geoffder/dometyl-keyboard/things/splaytyl/images/splaytyl_mt3.png

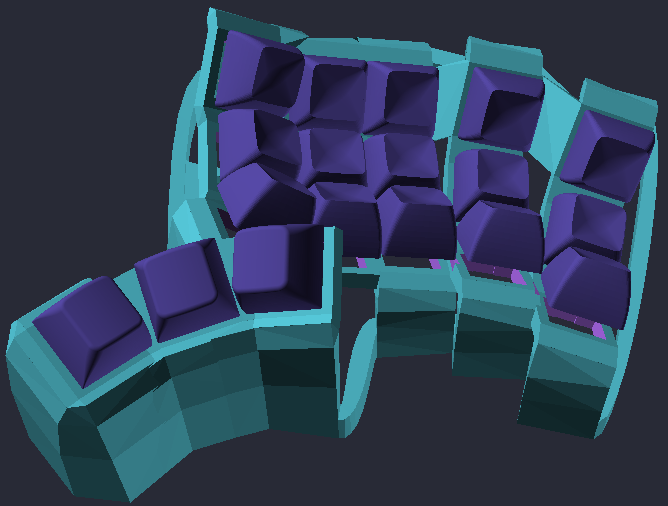
things/splaytyl/images/splaytyl_mt3.png
