geoffder/dometyl-keyboard/assets/sockets/mx_hotswap.stl

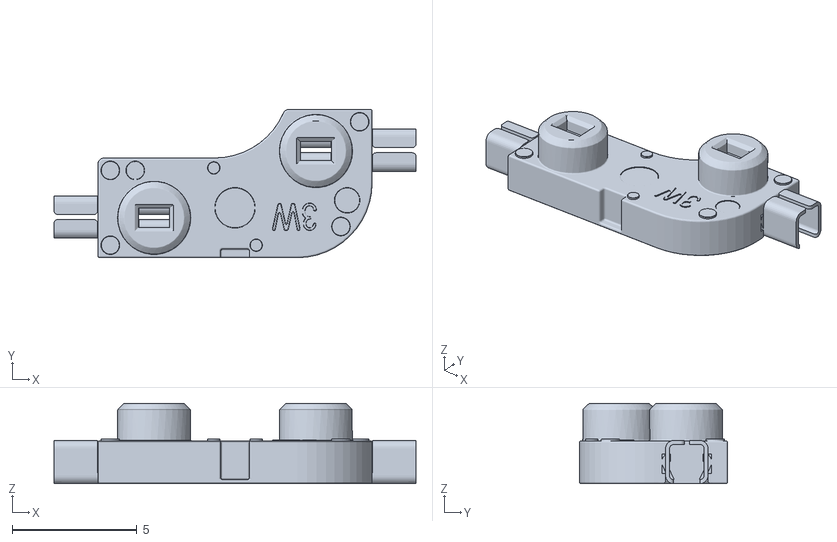
[picture p45: CAD file, 2021-09-09]
assets/sockets/mx_hotswap.stl
14.5 x 5.95 x 3.22
