geoffder/dometyl-keyboard/assets/switches/kailh_choc.stl

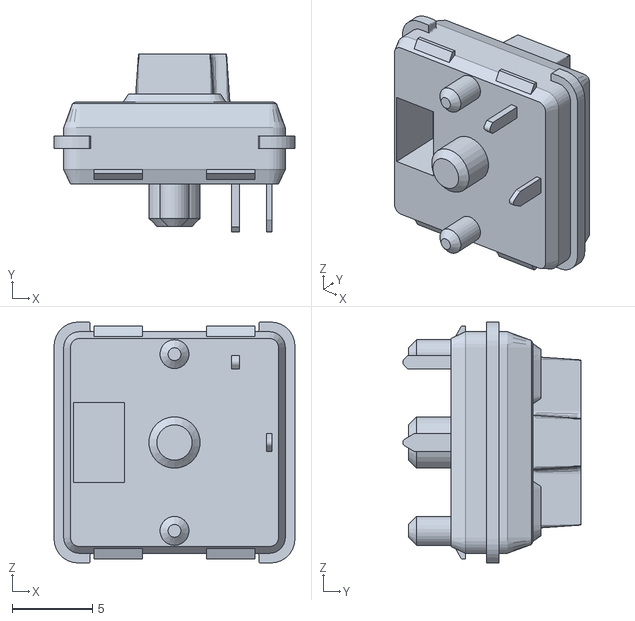
[picture p46: CAD file, 2021-09-06]
assets/switches/kailh_choc.stl
15.0 x 11.1 x 15.0
