geoffder/dometyl-keyboard/things/boards/choc_skeletyl/choc_skeletyl_right.stl

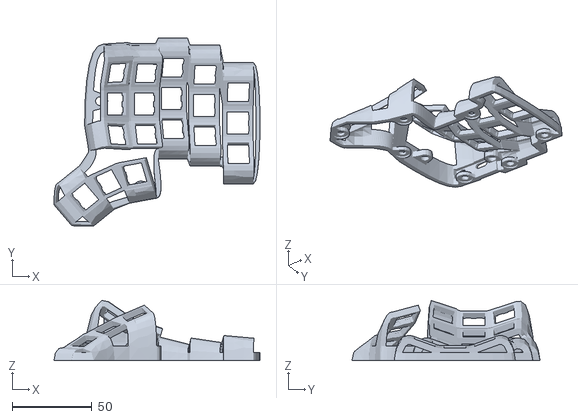
[picture p47: CAD file, 2021-11-04]
things/boards/choc_skeletyl/choc_skeletyl_right.stl
129.2 x 118.0 x 37.7
