geoffder/dometyl-keyboard/things/boards/choctyl/choctyl_hotswap_right.stl

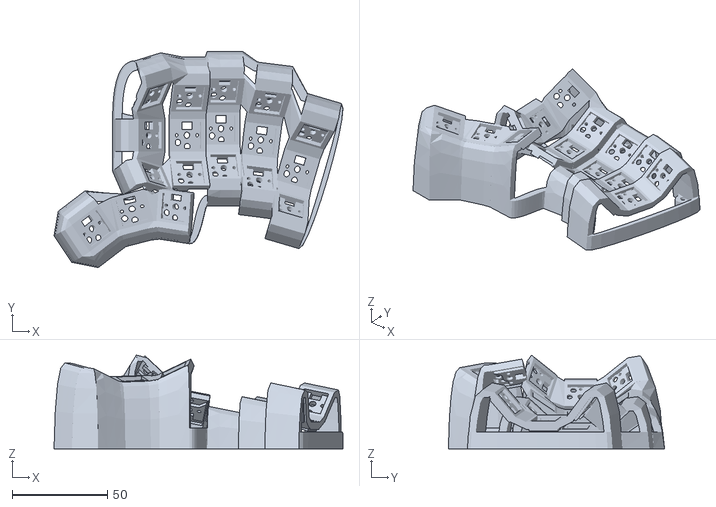
[picture p48: CAD file, 2021-11-10]
things/boards/choctyl/choctyl_hotswap_right.stl
151.9 x 113.6 x 49.3
