geoffder/dometyl-keyboard/things/boards/closed_splaytyl/closed_splaytyl_hotswap_left.stl

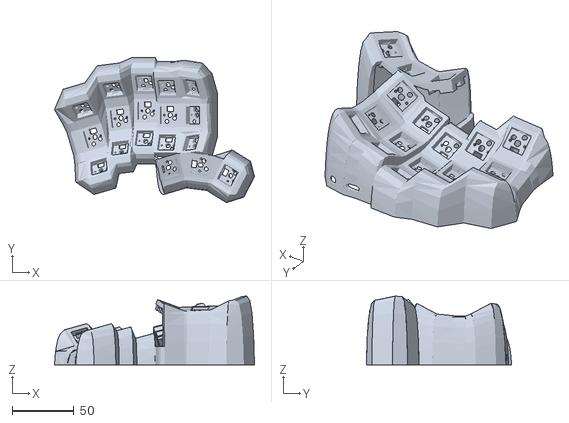
[picture p49: CAD file, 2021-09-25]
things/boards/closed_splaytyl/closed_splaytyl_hotswap_left.stl
161.5 x 117.4 x 55.7
