geoffder/dometyl-keyboard/things/boards/dartyl_choc/dartyl_mx.stl

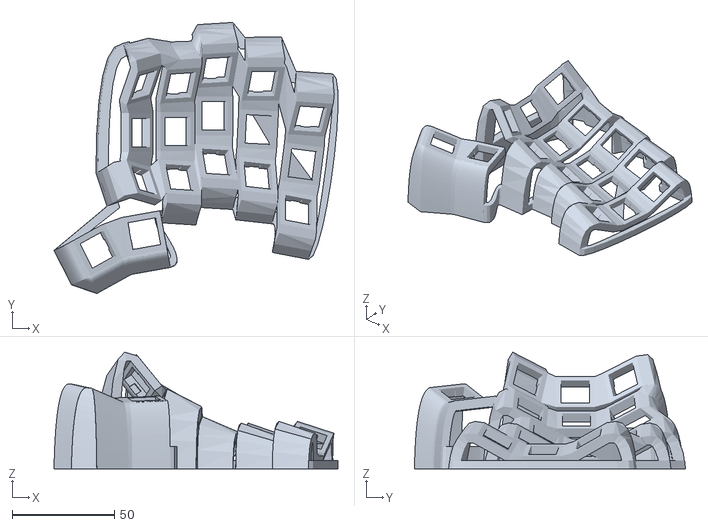
[picture p50: CAD file, 2021-11-20]
things/boards/dartyl_choc/dartyl_mx.stl
139.0 x 132.8 x 57.1
