geoffder/dometyl-keyboard/things/boards/dartyl_mx/dartyl_mx.stl

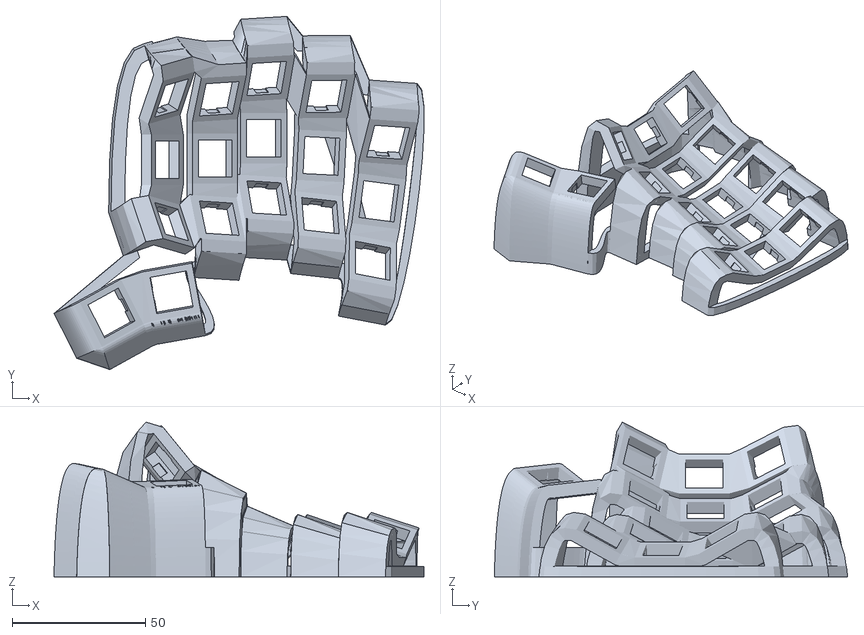
[picture p51: CAD file, 2021-11-20]
things/boards/dartyl_mx/dartyl_mx.stl
139.0 x 132.8 x 58.1
