geoffder/dometyl-keyboard/things/boards/niztyl/niztyl_right.stl

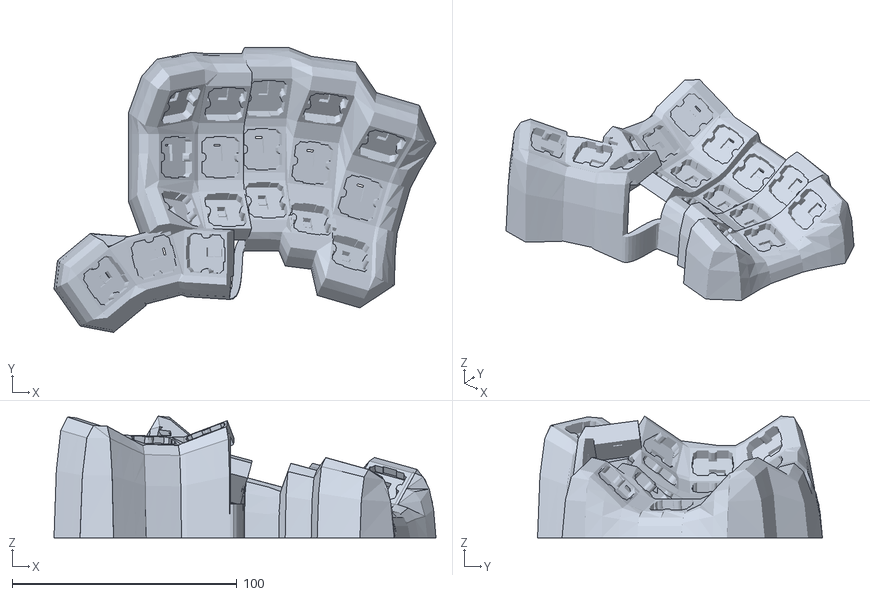
[picture p52: CAD file, 2021-11-09]
things/boards/niztyl/niztyl_right.stl
169.8 x 126.6 x 54.2
