geoffder/dometyl-keyboard/things/boards/splaytyl/splaytyl_tent_20deg_right.stl

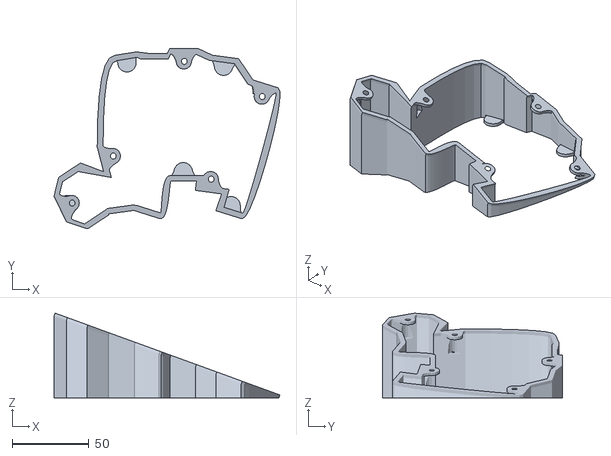
[picture p53: CAD file, 2021-10-03]
things/boards/splaytyl/splaytyl_tent_20deg_right.stl
147.0 x 117.4 x 55.1
