geoffder/dometyl-keyboard/things/choc_skeletyl/choc_skeletyl_right.stl

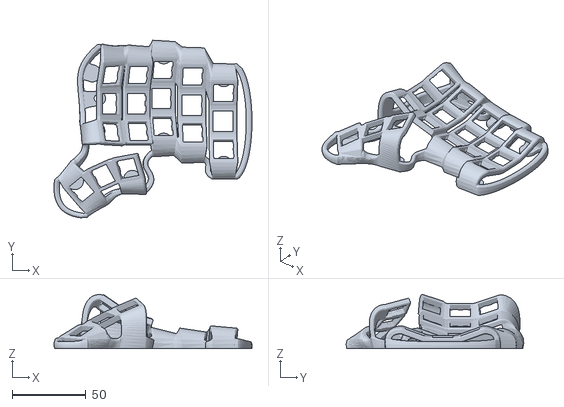
[picture p54: CAD file, 2023-01-07]
things/choc_skeletyl/choc_skeletyl_right.stl
134.2 x 120.4 x 36.9
