geoffder/dometyl-keyboard/things/dartyl_choc/usb_holder.stl

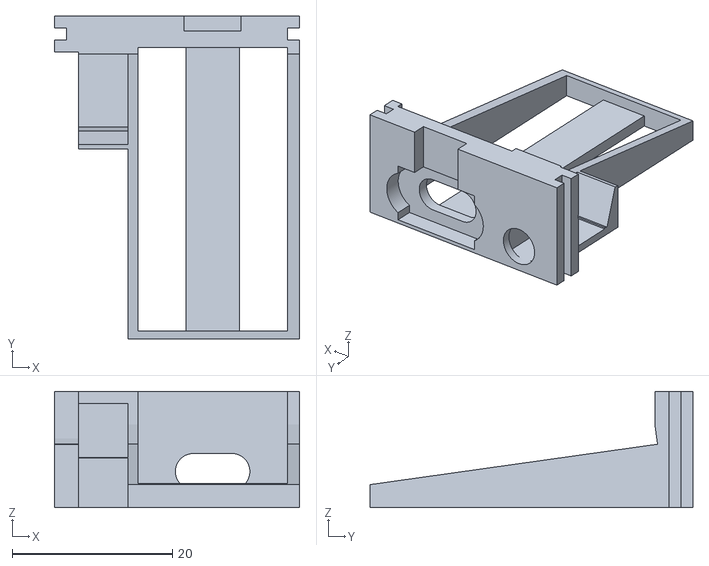
[picture p55: CAD file, 2021-11-20]
things/dartyl_choc/usb_holder.stl
30.6 x 40.3 x 14.5
