geoffder/dometyl-keyboard/things/dartyl_mx/MX_DES_Convex_012tol.stl

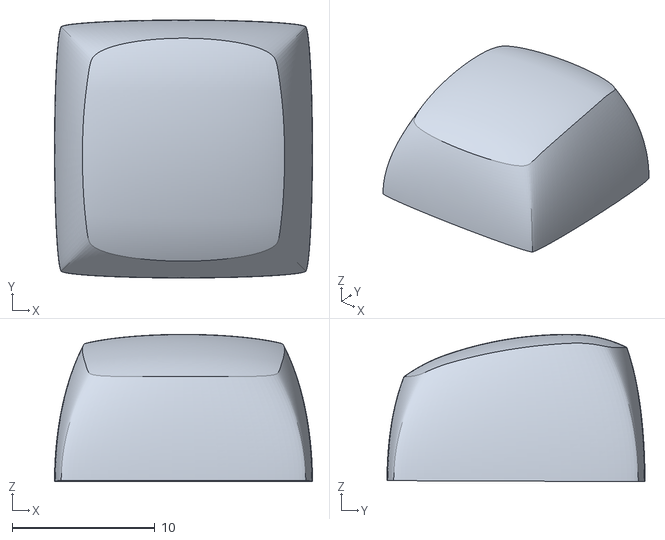
[picture p56: CAD file, 2021-11-20]
things/dartyl_mx/MX_DES_Convex_012tol.stl
18.1 x 18.1 x 10.3
