geoffder/dometyl-keyboard/things/niztyl/niztyl_base_right.stl

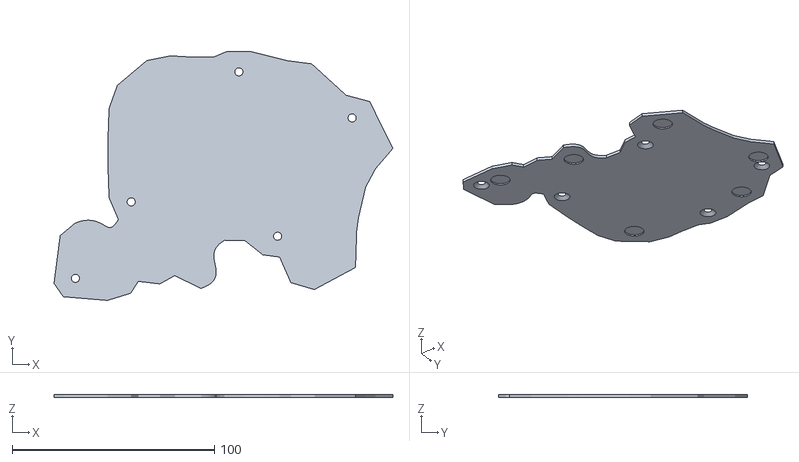
[picture p57: CAD file, 2023-01-07]
things/niztyl/niztyl_base_right.stl
167.8 x 123.1 x 1.65
