geoffder/dometyl-keyboard/things/splaytyl/splaytyl_base_right.stl

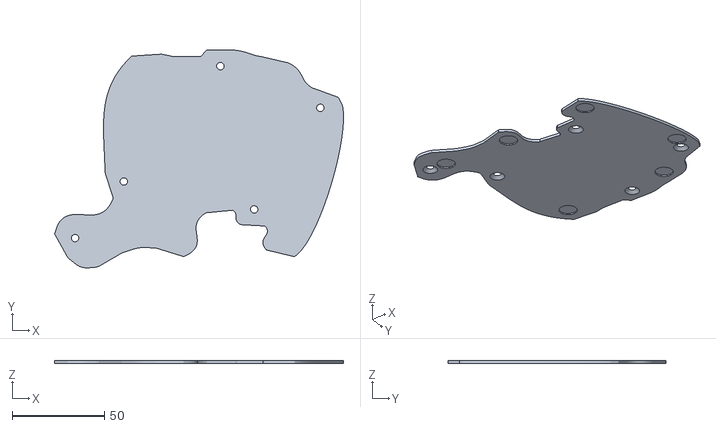
[picture p58: CAD file, 2023-01-07]
things/splaytyl/splaytyl_base_right.stl
156.3 x 117.7 x 1.65
