geoffder/dometyl-keyboard/assets/caps/KeyV2_cherry/cherry-R0.stl

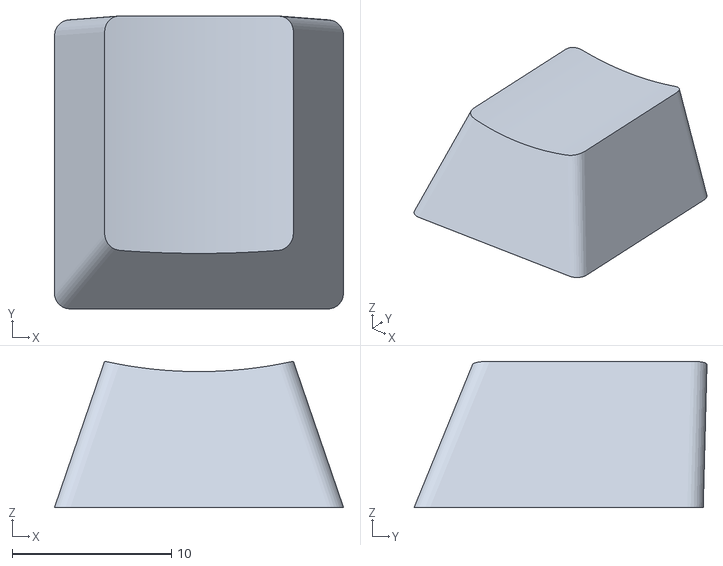
[picture p59: CAD file, 2021-09-16]
assets/caps/KeyV2_cherry/cherry-R0.stl
18.2 x 18.4 x 9.20
