geoffder/dometyl-keyboard/assets/caps/KeyV2_DSS/DSS-R3.stl

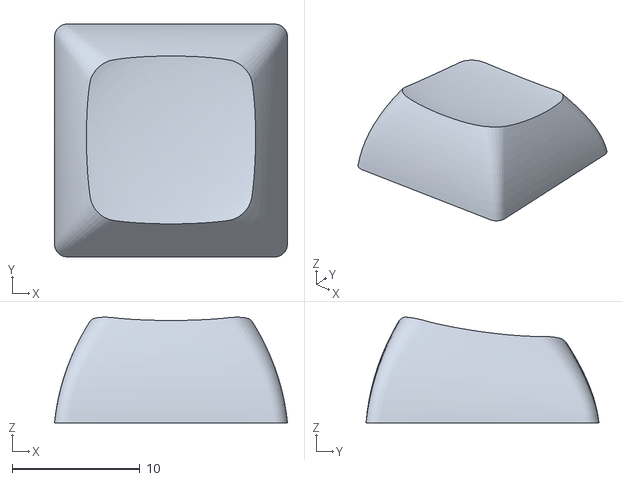
[picture p60: CAD file, 2021-09-17]
assets/caps/KeyV2_DSS/DSS-R3.stl
18.2 x 18.2 x 8.27
