geoffder/dometyl-keyboard/assets/caps/KeyV2_OEM/OEM-R5.stl

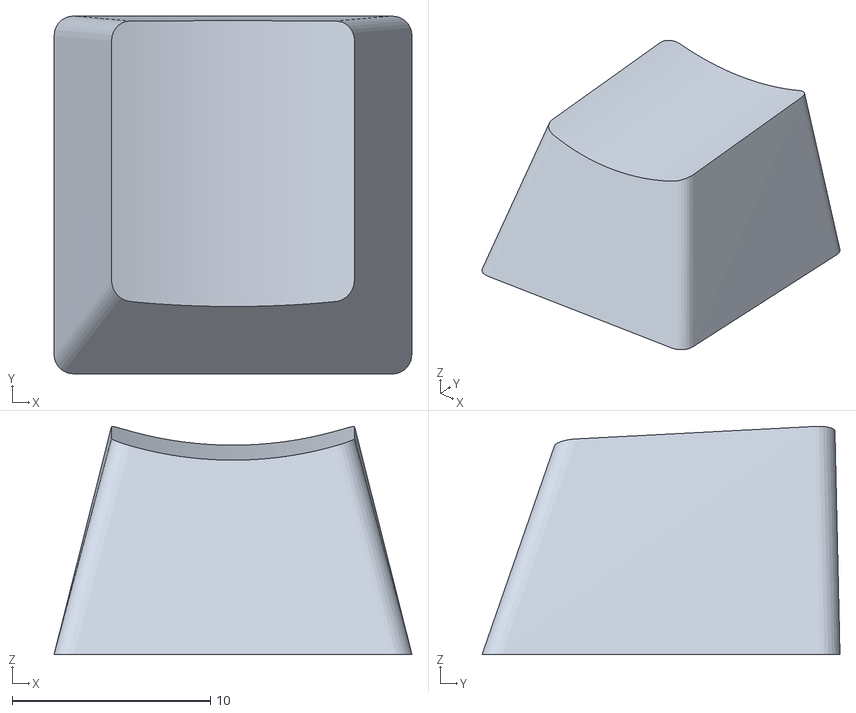
[picture p62: CAD file, 2021-09-16]
assets/caps/KeyV2_OEM/OEM-R5.stl
18.0 x 18.0 x 11.5
