geoffder/dometyl-keyboard/assets/caps/KeyV2_SA/SA-R4.stl

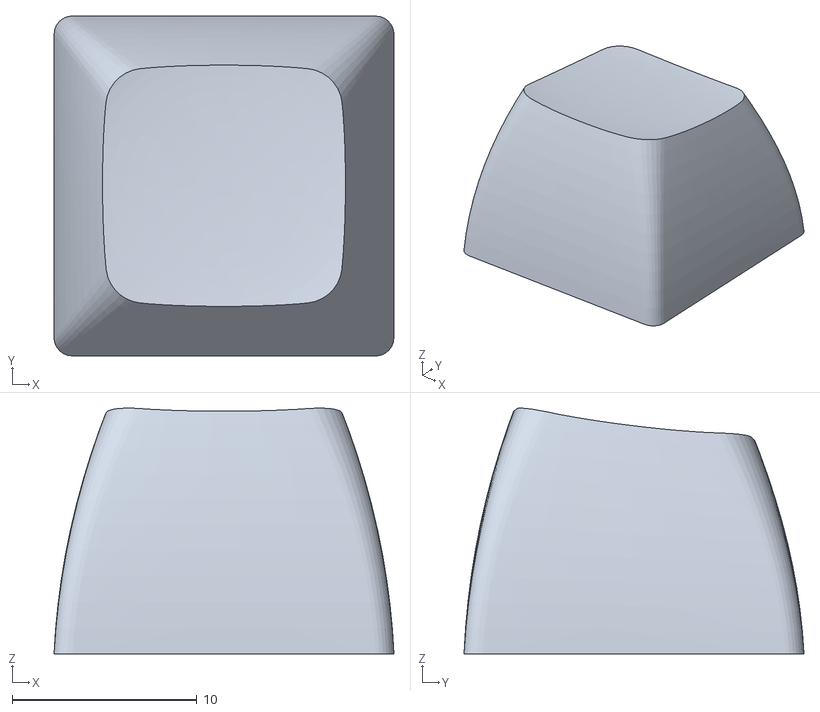
[picture p63: CAD file, 2021-09-16]
assets/caps/KeyV2_SA/SA-R4.stl
18.4 x 18.4 x 13.3
