geoffder/dometyl-keyboard/assets/caps/Pseudoku_DES/standard/DES-R3.stl

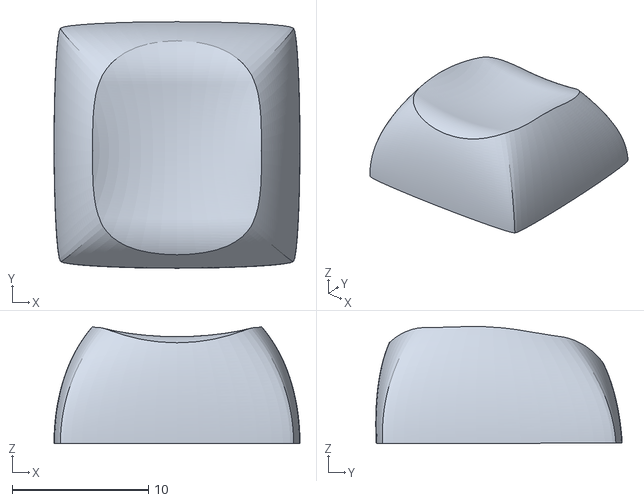
[picture p65: CAD file, 2021-09-27]
assets/caps/Pseudoku_DES/standard/DES-R3.stl
18.1 x 18.1 x 8.60
