geoffder/dometyl-keyboard/assets/mcu_holders/carbonfet/elite-c_holder.stl

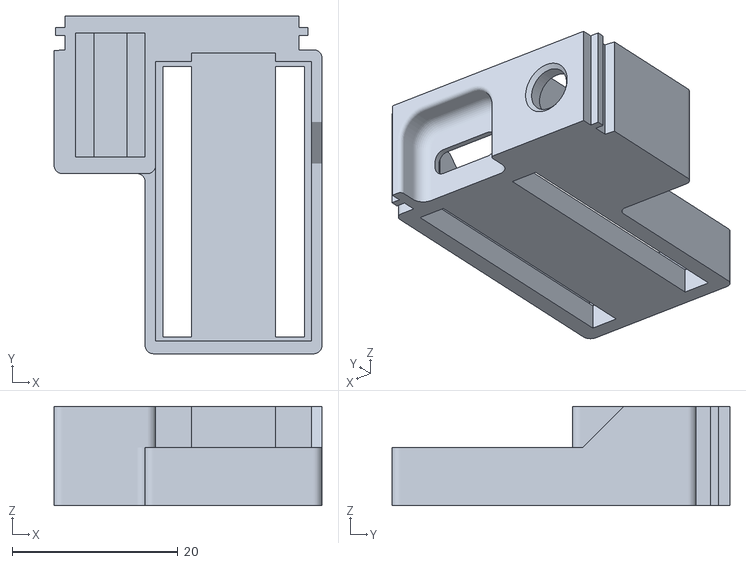
[picture p66: CAD file, 2021-08-31]
assets/mcu_holders/carbonfet/elite-c_holder.stl
32.3 x 40.8 x 12.0
