geoffder/dometyl-keyboard/assets/mcu_holders/dereknheiley/elite-c_holder.stl

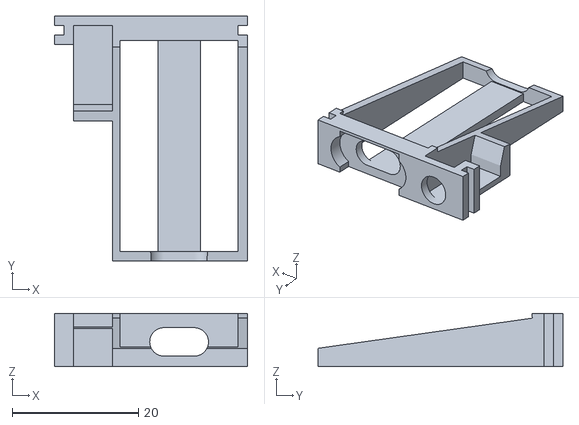
[picture p67: CAD file, 2021-09-01]
assets/mcu_holders/dereknheiley/elite-c_holder.stl
30.6 x 38.8 x 8.40
