geoffder/dometyl-keyboard/assets/other_dactyls/bastardkb_skeletyl_v3_v5.stl

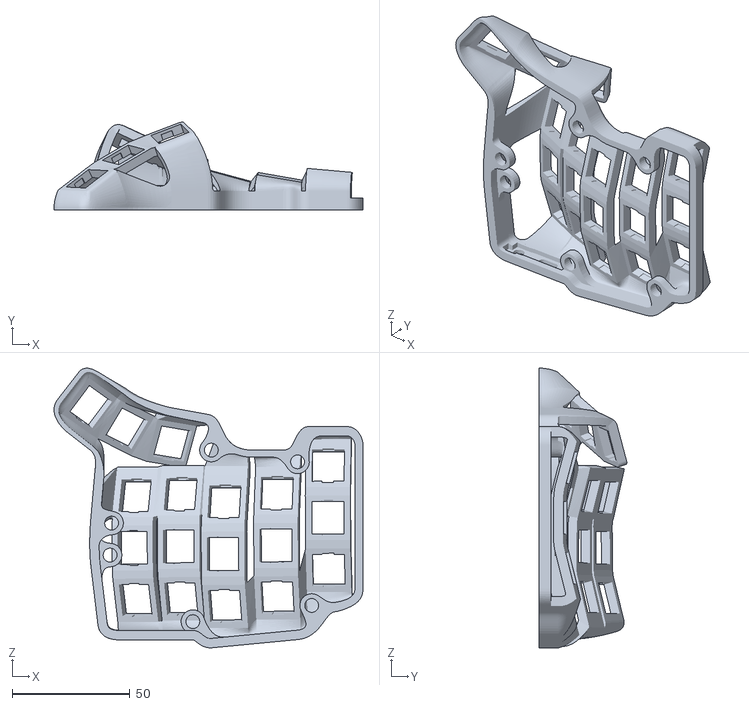
[picture p68: CAD file, 2021-08-22]
assets/other_dactyls/bastardkb_skeletyl_v3_v5.stl
131.3 x 37.3 x 118.8
