geoffder/dometyl-keyboard/assets/sockets/choc_hotswap.stl

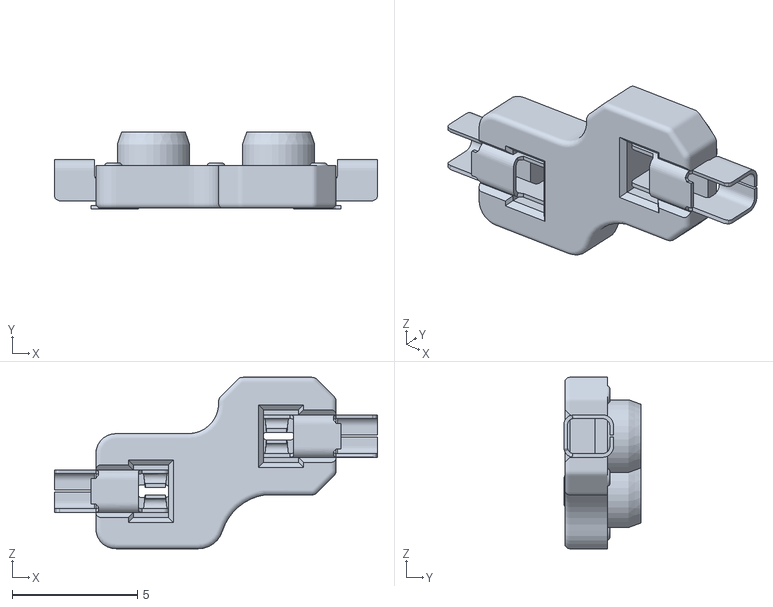
[picture p69: CAD file, 2021-09-06]
assets/sockets/choc_hotswap.stl
12.9 x 3.09 x 6.85
