geoffder/dometyl-keyboard/things/boards/choc_skeletyl/choc_skeletyl_hotswap_left.stl

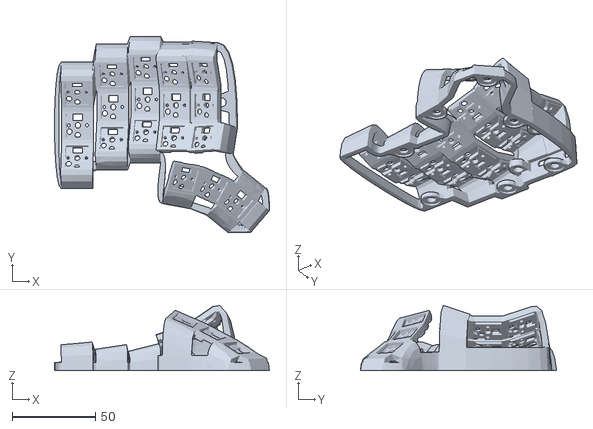
[picture p70: CAD file, 2021-11-04]
things/boards/choc_skeletyl/choc_skeletyl_hotswap_left.stl
129.2 x 118.0 x 39.2
