geoffder/dometyl-keyboard/things/boards/dartyl_choc/dartyl_choc.stl

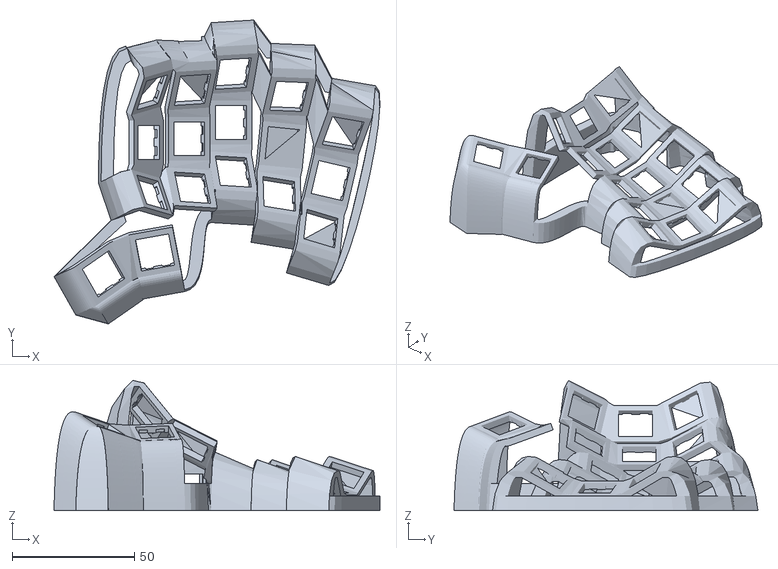
[picture p72: CAD file, 2021-11-10]
things/boards/dartyl_choc/dartyl_choc.stl
133.2 x 124.2 x 53.2
