geoffder/dometyl-keyboard/things/boards/niztyl/niztyl_tent_30deg_right.stl

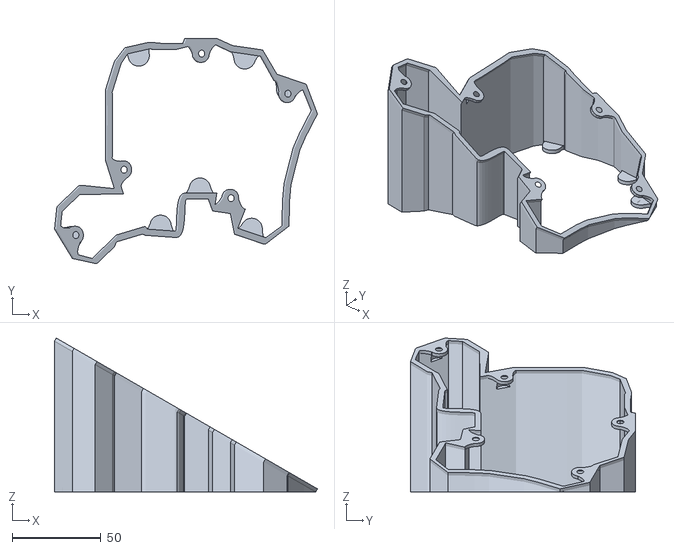
[picture p73: CAD file, 2021-11-09]
things/boards/niztyl/niztyl_tent_30deg_right.stl
148.0 x 126.6 x 86.6
