geoffder/dometyl-keyboard/things/boards/splaytyl/splaytyl_tent_30deg_right.stl

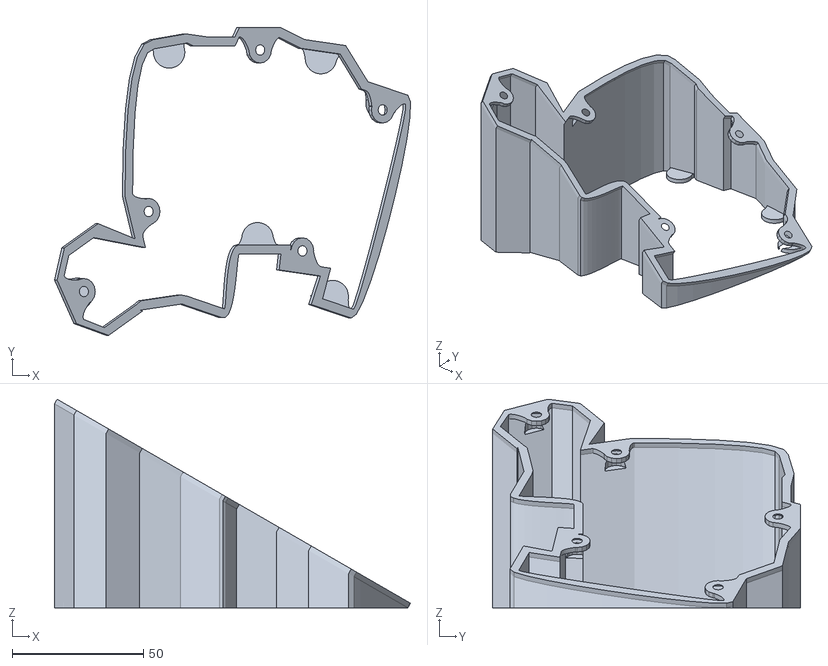
[picture p74: CAD file, 2021-10-03]
things/boards/splaytyl/splaytyl_tent_30deg_right.stl
135.8 x 117.4 x 79.6
