geoffder/dometyl-keyboard/assets/caps/KeyV2_cherry/cherry-R3.stl

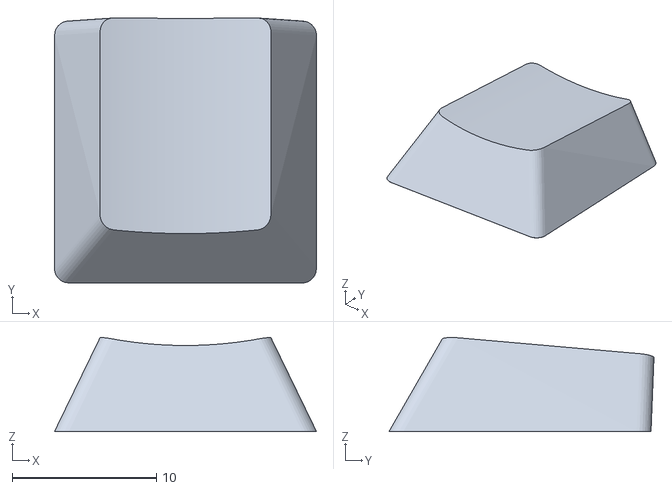
[picture p75: CAD file, 2021-09-16]
assets/caps/KeyV2_cherry/cherry-R3.stl
18.2 x 18.4 x 6.52
