geoffder/dometyl-keyboard/assets/caps/KeyV2_matty3/matty3-deep-R1.stl

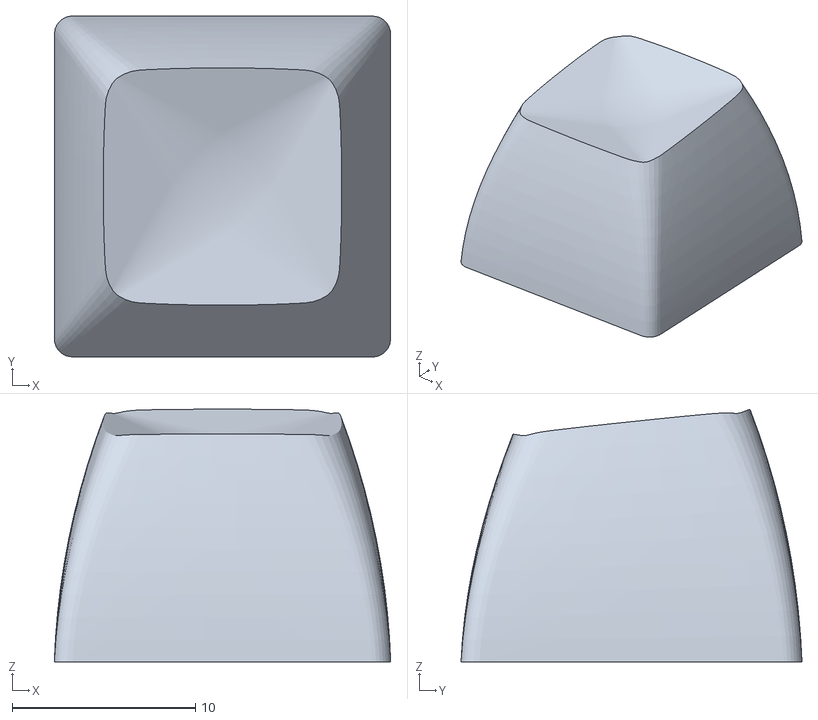
[picture p76: CAD file, 2021-09-16]
assets/caps/KeyV2_matty3/matty3-deep-R1.stl
18.3 x 18.6 x 13.8
