geoffder/dometyl-keyboard/assets/caps/KeyV2_OEM/OEM-R1.stl

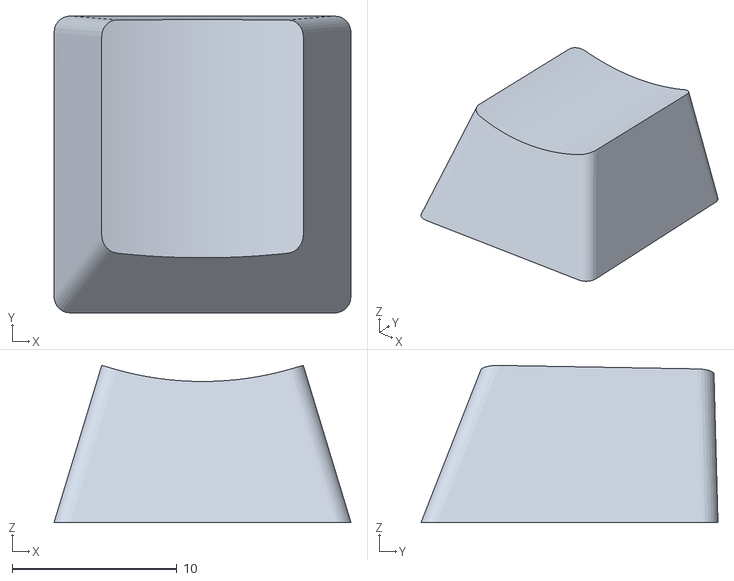
[picture p77: CAD file, 2021-09-16]
assets/caps/KeyV2_OEM/OEM-R1.stl
18.0 x 18.0 x 9.55
