geoffder/dometyl-keyboard/assets/caps/KeyV2_SA/SA-R0.stl

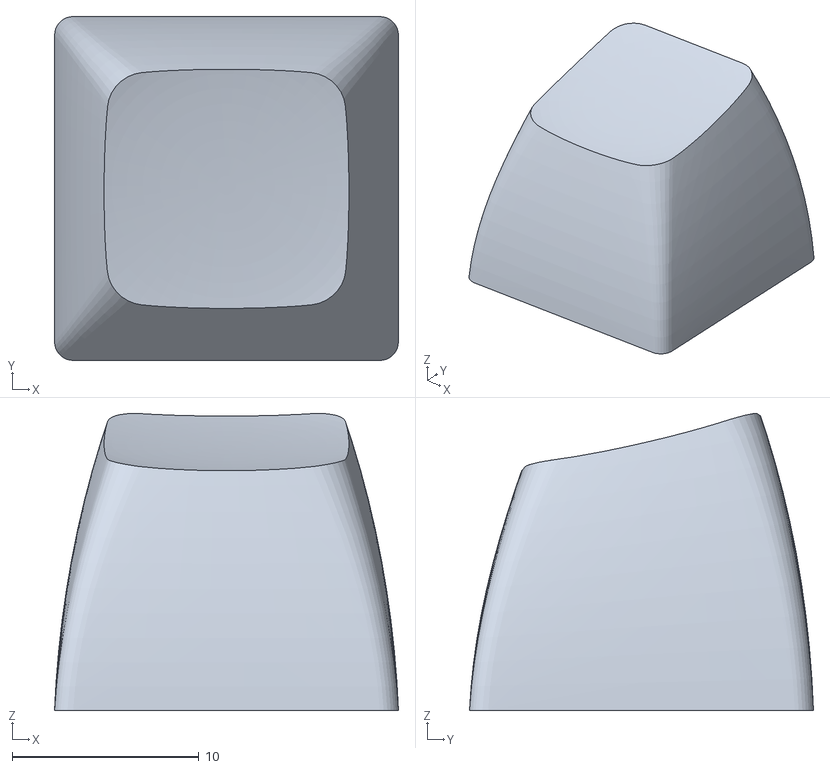
[picture p78: CAD file, 2021-09-16]
assets/caps/KeyV2_SA/SA-R0.stl
18.4 x 18.4 x 15.9
