geoffder/dometyl-keyboard/assets/caps/Pseudoku_Chicago/Chicago-R2-R4.stl

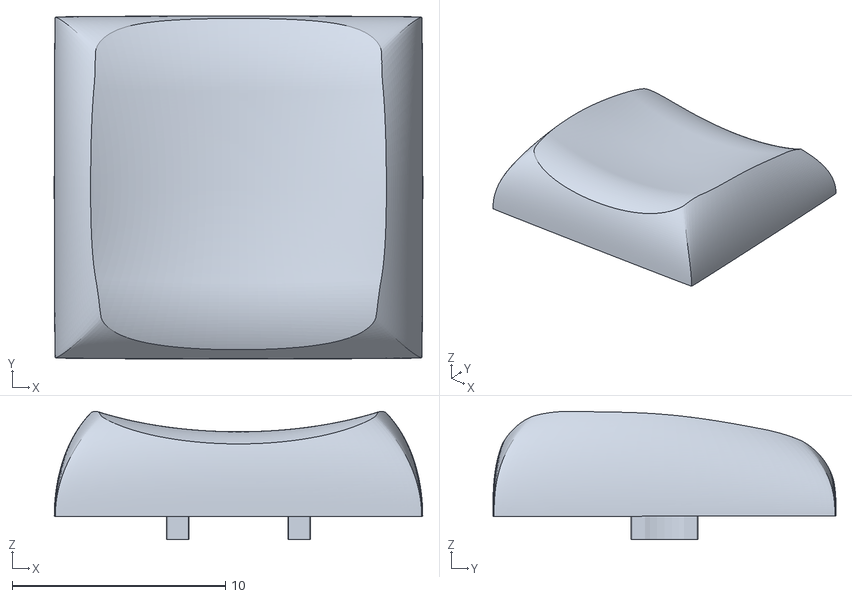
[picture p79: CAD file, 2021-09-27]
assets/caps/Pseudoku_Chicago/Chicago-R2-R4.stl
17.3 x 16.1 x 6.02
