geoffder/dometyl-keyboard/assets/caps/Pseudoku_DES/standard/DES-R4.stl

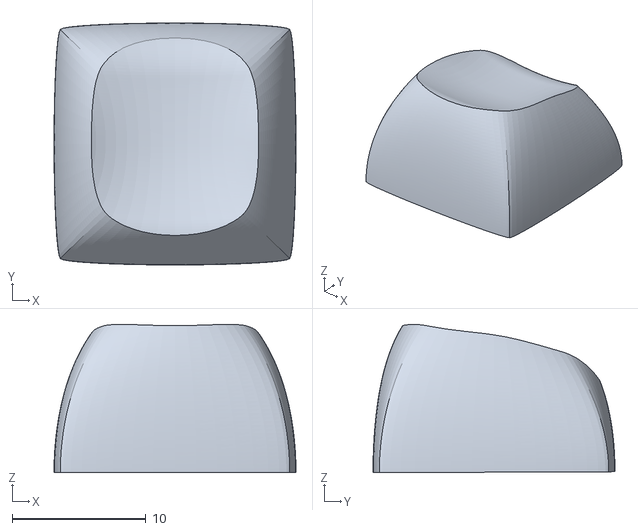
[picture p80: CAD file, 2021-09-27]
assets/caps/Pseudoku_DES/standard/DES-R4.stl
18.1 x 18.1 x 11.1
