geoffder/dometyl-keyboard/assets/caps/Pseudoku_DES/thumb/DES-kyria-R1T2.stl

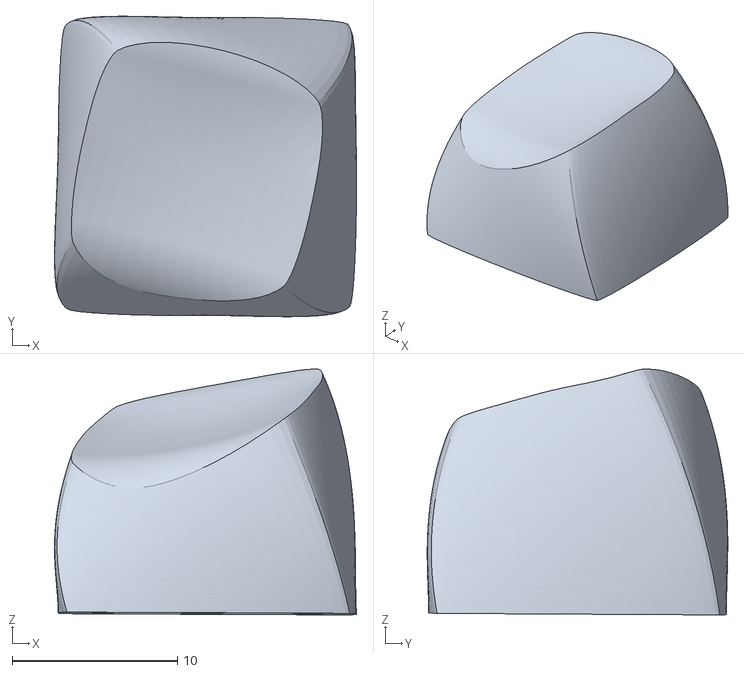
[picture p81: CAD file, 2021-09-27]
assets/caps/Pseudoku_DES/thumb/DES-kyria-R1T2.stl
18.3 x 18.2 x 14.9
