geoffder/dometyl-keyboard/assets/mcu_holders/carbonfet/shim.stl

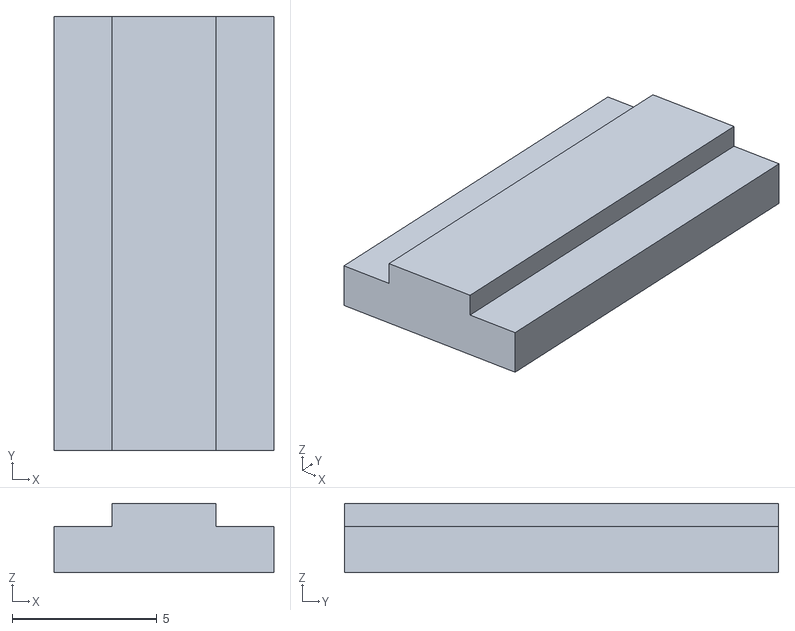
[picture p82: CAD file, 2021-08-31]
assets/mcu_holders/carbonfet/shim.stl
7.60 x 15.0 x 2.40
