geoffder/dometyl-keyboard/things/boards/choctyl/choctyl_plate_6x3mag_right.stl

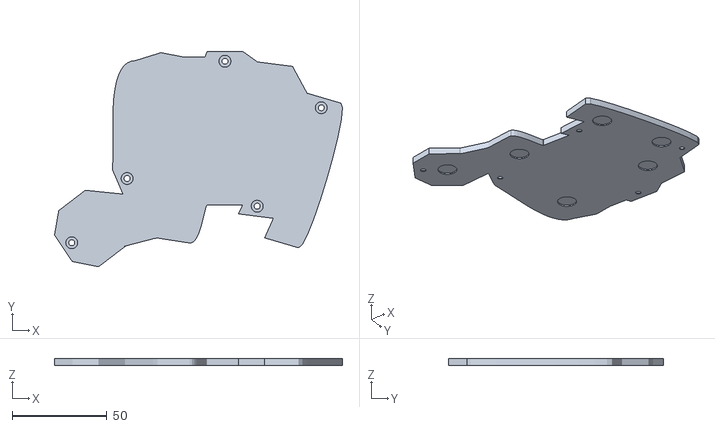
[picture p83: CAD file, 2021-11-10]
things/boards/choctyl/choctyl_plate_6x3mag_right.stl
151.9 x 113.6 x 3.80
