geoffder/dometyl-keyboard/things/boards/niztyl/niztyl_base_right.stl

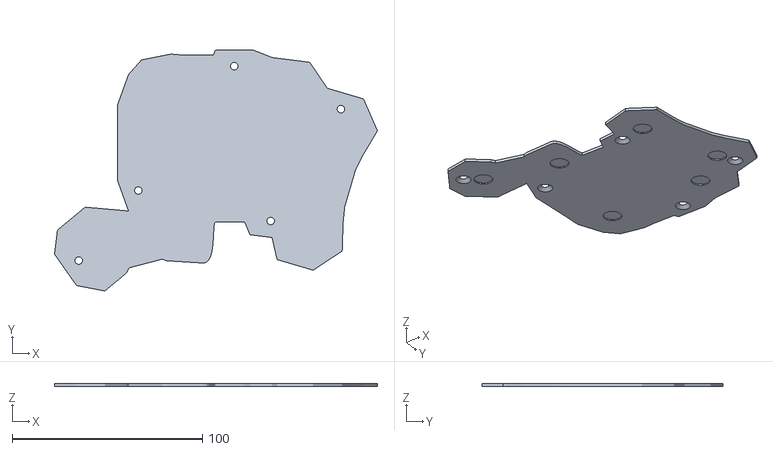
[picture p84: CAD file, 2021-11-09]
things/boards/niztyl/niztyl_base_right.stl
169.8 x 126.6 x 1.65
