geoffder/dometyl-keyboard/assets/caps/KeyV2_cherry/cherry-R2.stl

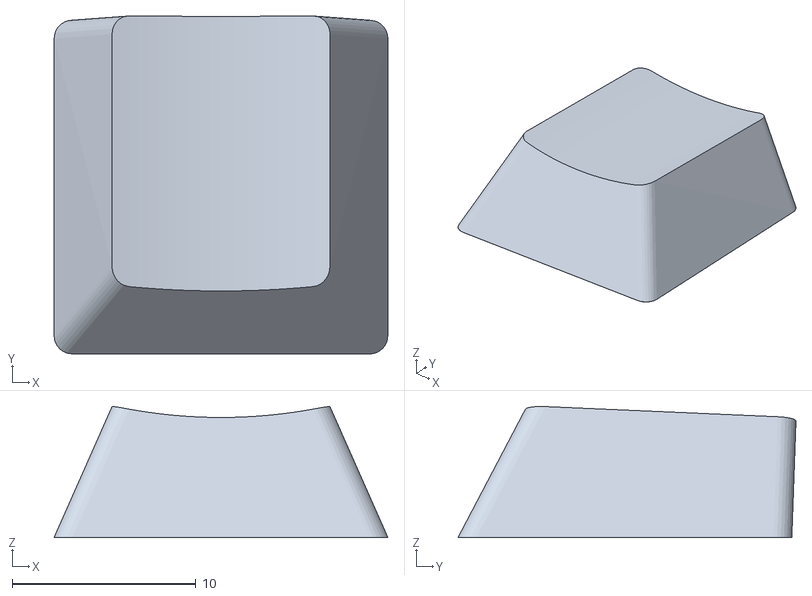
[picture p86: CAD file, 2021-09-16]
assets/caps/KeyV2_cherry/cherry-R2.stl
18.2 x 18.4 x 7.13
