geoffder/dometyl-keyboard/assets/caps/KeyV2_OEM/OEM-R2.stl

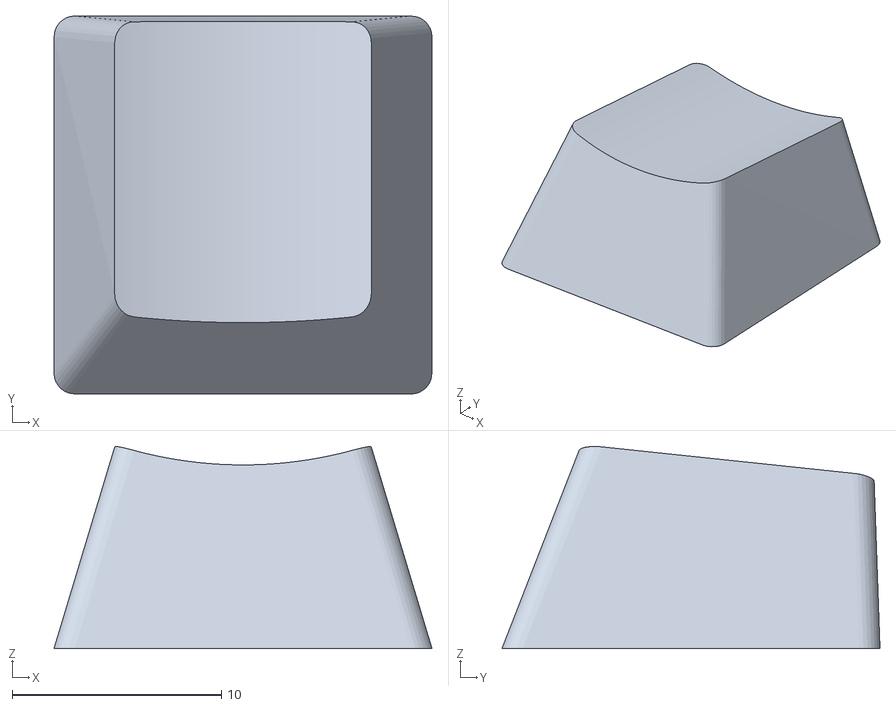
[picture p87: CAD file, 2021-09-16]
assets/caps/KeyV2_OEM/OEM-R2.stl
18.0 x 18.0 x 9.65
