geoffder/dometyl-keyboard/assets/caps/Pseudoku_Chicago/Chicago-thumb-1_5u.stl

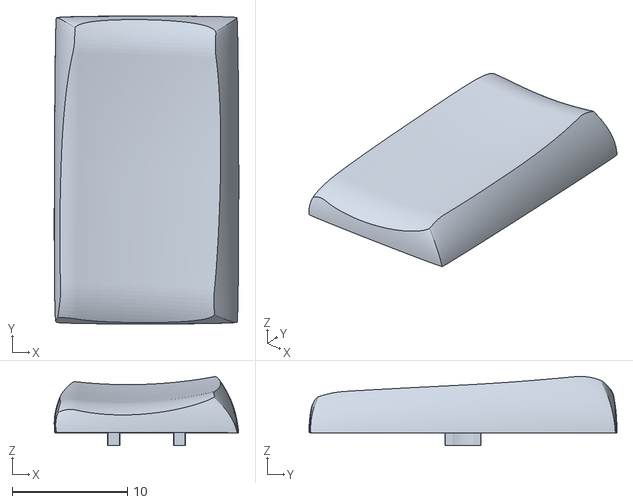
[picture p88: CAD file, 2021-09-27]
assets/caps/Pseudoku_Chicago/Chicago-thumb-1_5u.stl
16.0 x 26.7 x 5.99
