geoffder/dometyl-keyboard/assets/caps/Pseudoku_DES/standard/DES-R2.stl

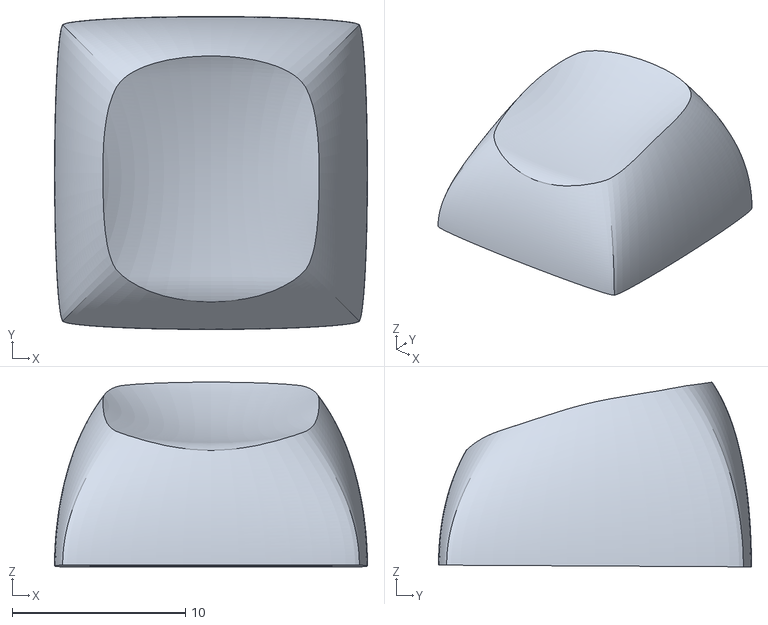
[picture p89: CAD file, 2021-09-27]
assets/caps/Pseudoku_DES/standard/DES-R2.stl
18.1 x 18.1 x 10.7
