geoffder/dometyl-keyboard/things/boards/choctyl/choctyl_30deg_tent_right.stl

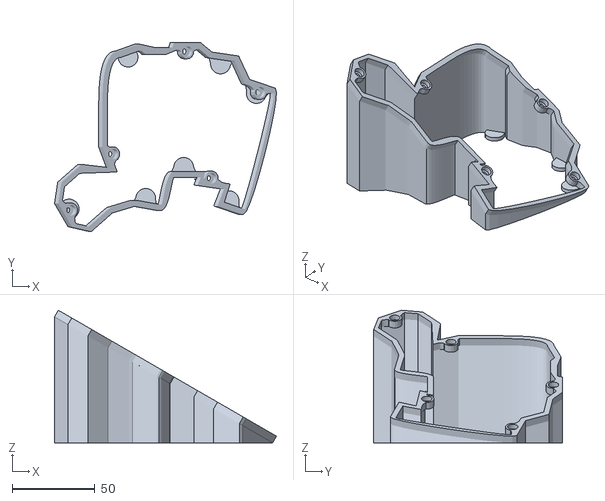
[picture p90: CAD file, 2021-11-10]
things/boards/choctyl/choctyl_30deg_tent_right.stl
133.8 x 113.6 x 79.9
