geoffder/dometyl-keyboard/things/boards/closed_splaytyl/closed_splaytyl_right.stl

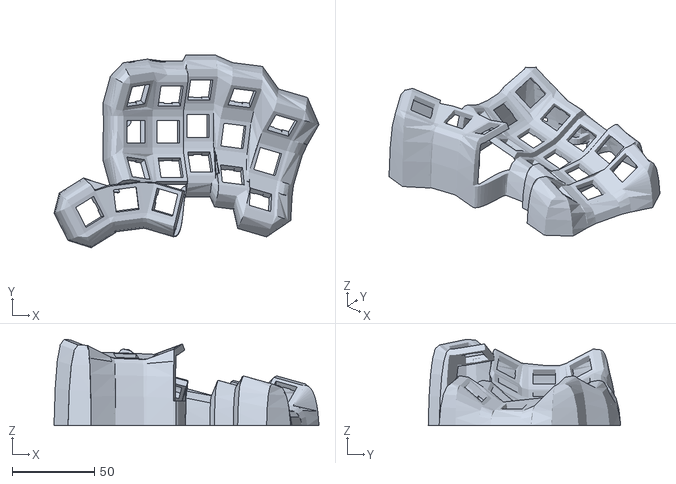
[picture p91: CAD file, 2021-09-25]
things/boards/closed_splaytyl/closed_splaytyl_right.stl
161.5 x 117.4 x 52.7
