geoffder/dometyl-keyboard/things/boards/splaytyl/splaytyl_base_right.stl

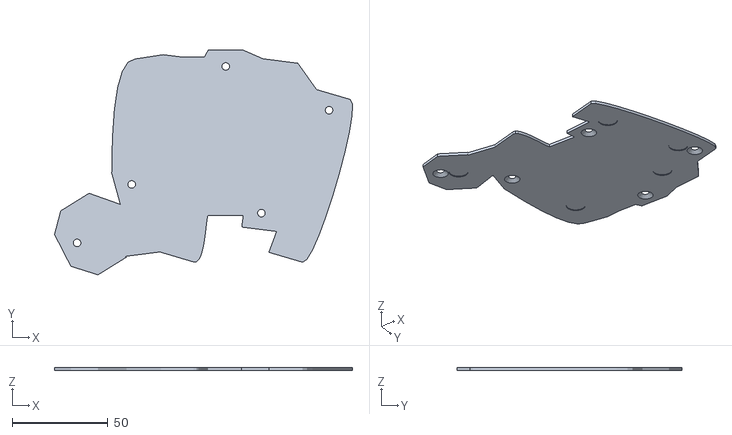
[picture p92: CAD file, 2021-09-29]
things/boards/splaytyl/splaytyl_base_right.stl
155.7 x 117.4 x 1.65
