geoffder/dometyl-keyboard/assets/caps/KeyV2_DSS/DSS-R4.stl

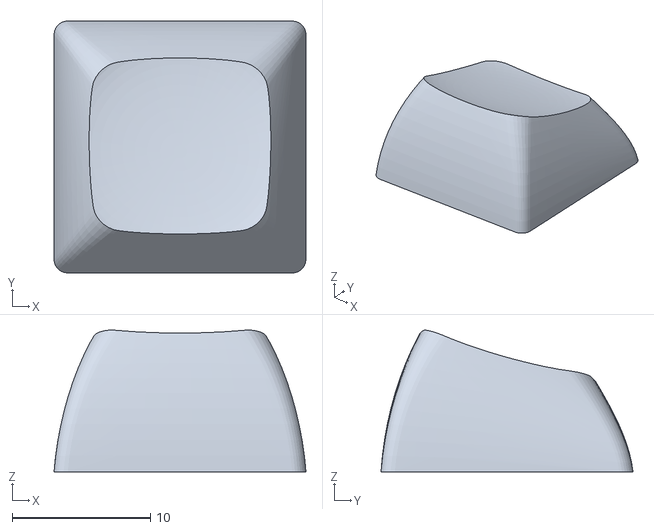
[picture p93: CAD file, 2021-09-17]
assets/caps/KeyV2_DSS/DSS-R4.stl
18.2 x 18.2 x 10.3
