geoffder/dometyl-keyboard/assets/caps/KeyV2_matty3/matty3-deep-R0.stl

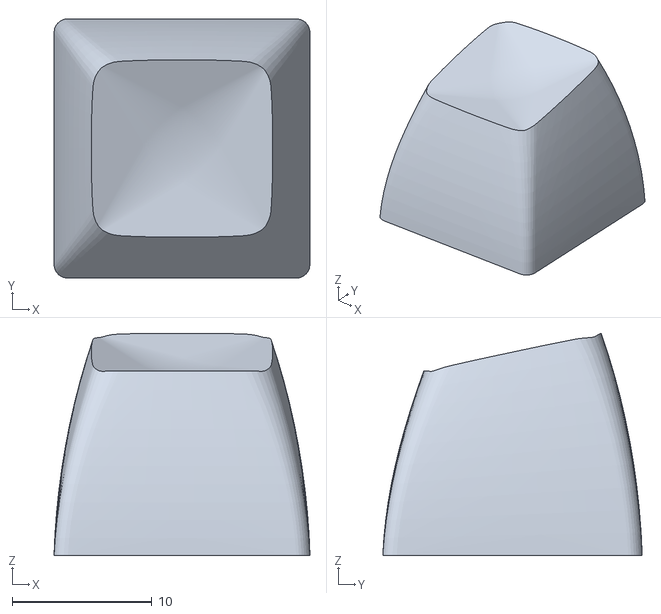
[picture p94: CAD file, 2021-09-16]
assets/caps/KeyV2_matty3/matty3-deep-R0.stl
18.3 x 18.6 x 15.9
