geoffder/dometyl-keyboard/assets/caps/Pseudoku_Chicago/Chicago-R3-flat.stl

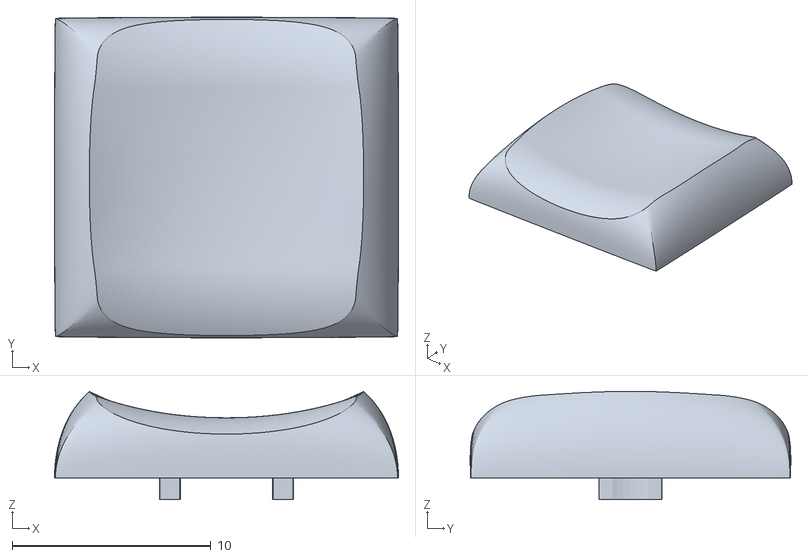
[picture p95: CAD file, 2021-09-27]
assets/caps/Pseudoku_Chicago/Chicago-R3-flat.stl
17.3 x 16.1 x 5.45
