geoffder/dometyl-keyboard/assets/caps/Pseudoku_DES/standard/DES-R1.stl

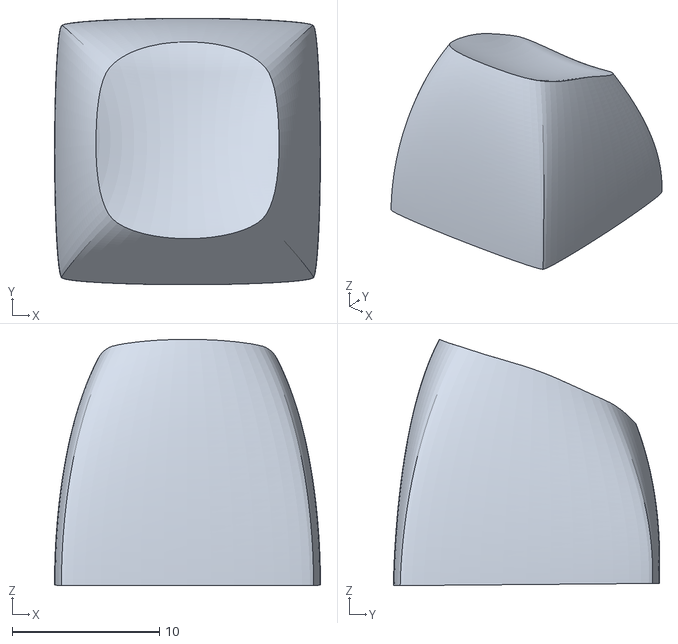
[picture p96: CAD file, 2021-09-27]
assets/caps/Pseudoku_DES/standard/DES-R1.stl
18.1 x 18.1 x 16.7
