geoffder/dometyl-keyboard/things/boards/choctyl/choctyl_20deg_tent_right.stl

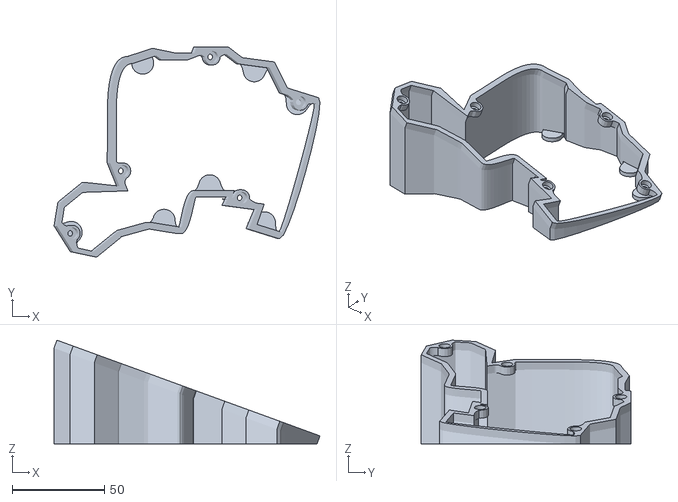
[picture p97: CAD file, 2021-11-10]
things/boards/choctyl/choctyl_20deg_tent_right.stl
144.3 x 113.6 x 56.3
