geoffder/dometyl-keyboard/things/boards/closed_splaytyl/closed_splaytyl_30deg_tent_right.stl

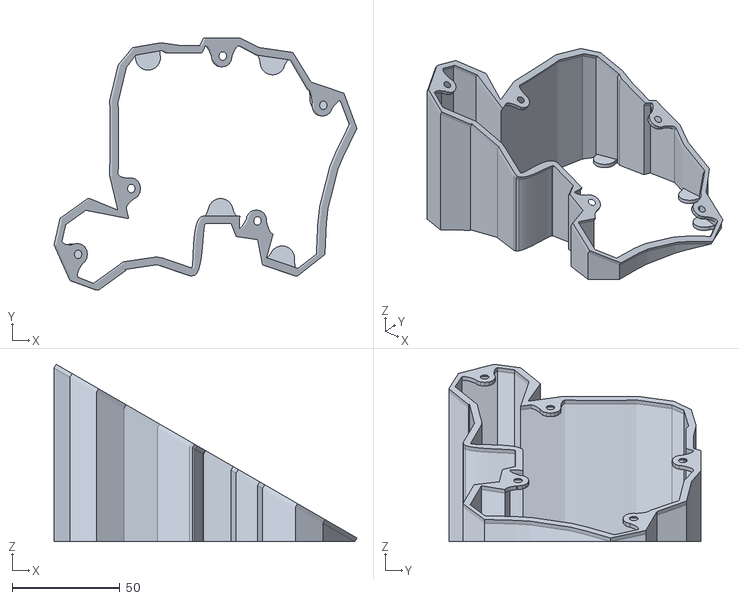
[picture p98: CAD file, 2021-09-25]
things/boards/closed_splaytyl/closed_splaytyl_30deg_tent_right.stl
140.9 x 117.4 x 82.5
