geoffder/dometyl-keyboard/things/boards/splaytyl/splaytyl_right.stl

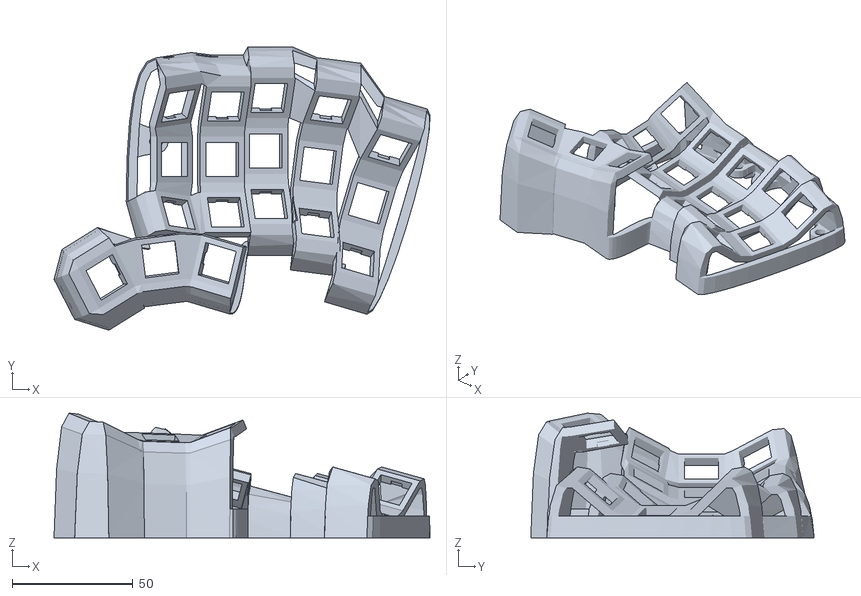
[picture p99: CAD file, 2021-09-29]
things/boards/splaytyl/splaytyl_right.stl
155.7 x 117.4 x 51.7
