geoffder/dometyl-keyboard/things/boards/splaytyl/splaytyl_hotswap_left.stl

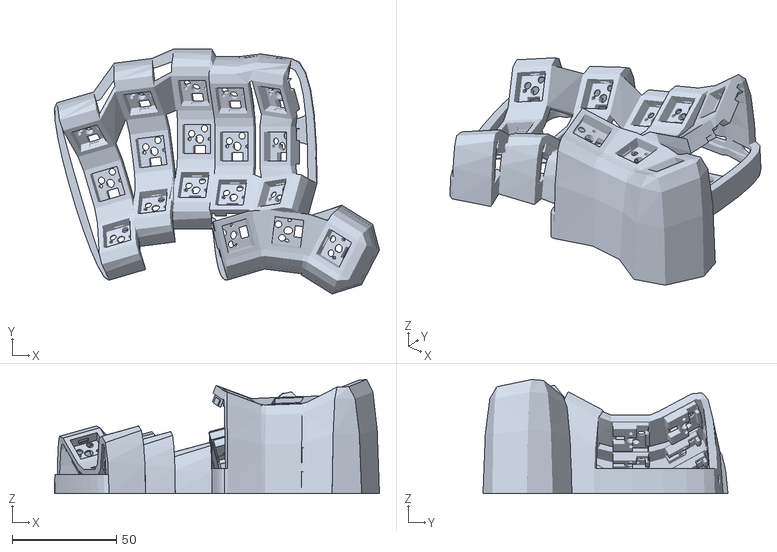
[picture p101: CAD file, 2021-09-29]
things/boards/splaytyl/splaytyl_hotswap_left.stl
155.7 x 117.4 x 54.7
