geoffder/dometyl-keyboard/things/boards/choctyl/choctyl_right.stl

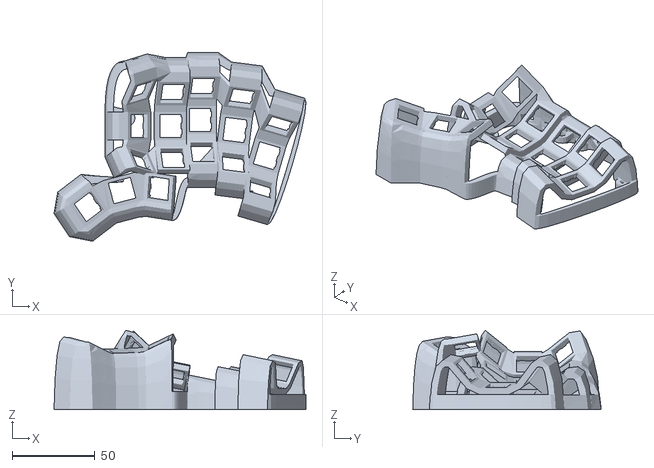
[picture p102: CAD file, 2021-11-10]
things/boards/choctyl/choctyl_right.stl
151.9 x 113.6 x 47.8
